rossumur/Zorkduino/zorkduino/zdFont.h

// 256 char inverted set
0x00,0x18,0x03,0x18,0x18,0x00,0x03,0xc0,
0x01,0x00,0x80,0x0f,0xf0,0xff,0x00,0x00,
0x24,0x28,0x08,0x10,0x10,0x10,0x08,0x08,
0x08,0x08,0x08,0x00,0x00,0x00,0x00,0x00,
0x00,0x00,0x00,0x00,0x18,0x00,0x1c,0x00,
0x00,0x00,0x00,0x00,0x00,0x00,0x00,0x00,
0x00,0x00,0x00,0x00,0x00,0x00,0x00,0x00,
0x00,0x00,0x00,0x00,0x06,0x00,0x60,0x00,
0x00,0x00,0x00,0x00,0x00,0x00,0x00,0x00,
0x00,0x00,0x00,0x00,0x00,0x00,0x00,0x00,
0x00,0x00,0x00,0x00,0x00,0x00,0x00,0x00,
0x00,0x00,0x00,0x00,0x00,0x00,0x00,0x00,
0x00,0x00,0x00,0x00,0x00,0x00,0x00,0x00,
0x00,0x00,0x00,0x00,0x00,0x00,0x00,0x00,
0x00,0x00,0x00,0x00,0x00,0x00,0x00,0x00,
0x00,0x00,0x00,0x00,0x18,0x00,0x08,0x10,
0xff,0xe7,0xfc,0xe7,0xe7,0xff,0xfc,0x3f,
0xfe,0xff,0x7f,0xf0,0x0f,0x00,0xff,0xff,
0xff,0xff,0xff,0xe7,0xff,0xff,0x3f,0xff,
0xe7,0x0f,0xe7,0x87,0xff,0xff,0xff,0xff,
0xff,0xff,0xff,0xff,0xe7,0xff,0xe3,0xff,
0xff,0xff,0xff,0xff,0xff,0xff,0xff,0xff,
0xff,0xff,0xff,0xff,0xff,0xff,0xff,0xff,
0xff,0xff,0xff,0xff,0xf9,0xff,0x9f,0xff,
0xff,0xff,0xff,0xff,0xff,0xff,0xff,0xff,
0xff,0xff,0xff,0xff,0xff,0xff,0xff,0xff,
0xff,0xff,0xff,0xff,0xff,0xff,0xff,0xff,
0xff,0xff,0xff,0xff,0xff,0xff,0xff,0xff,
0xff,0xff,0xff,0xff,0xff,0xff,0xff,0xff,
0xff,0xff,0xff,0xff,0xff,0xff,0xff,0xff,
0xff,0xff,0xff,0xff,0xff,0xff,0xff,0xff,
0xff,0xff,0xff,0xff,0xe7,0xff,0xf7,0xef,

0x00,0x18,0x03,0x18,0x18,0x00,0x07,0xe0,
0x03,0x00,0xc0,0x0f,0xf0,0xff,0x00,0x00,
0x00,0x00,0x10,0x08,0x08,0x08,0x14,0x14,
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
0xff,0xff,0xff,0xff,0xff,0xff,0xff,0xff,
0xff,0xff,0xff,0xff,0xff,0xff,0xff,0xff,
0xff,0xff,0xff,0xff,0xff,0xff,0xff,0xff,
0xff,0xff,0xff,0xff,0xff,0xff,0xff,0x83,
0xff,0xff,0xc3,0xff,0xff,0xff,0xff,0xff,
0x9f,0xf9,0xff,0xff,0xff,0xff,0xff,0xff,
0xff,0x87,0xff,0xff,0xe7,0xff,0xff,0xff,
