rossumur/Zorkduino/zorkduino/zdLogofont.h

// 200x72 256 chars
0x00,0x00,0x00,0x00,0x00,0x00,0x00,0x00,
0x00,0x00,0x00,0x00,0x00,0x00,0x00,0x00,
0x00,0x00,0x00,0x00,0x02,0xf8,0xc4,0x00,
0x00,0x00,0x00,0x00,0x00,0x00,0x00,0x00,
0x00,0x00,0x00,0x7c,0x80,0x00,0x00,0x00,
0x00,0x00,0x00,0x00,0x00,0x04,0x4f,0xf0,
0x00,0x00,0x00,0x00,0x08,0xef,0xff,0x7e,
0x5b,0xd6,0x00,0x04,0x04,0x17,0xc1,0xff,
0x81,0x64,0x4b,0xfb,0x39,0xfa,0x06,0xf7,
0xf8,0x00,0x10,0xe2,0x00,0x0b,0xed,0x8f,
0x57,0xc0,0xf4,0x52,0xf0,0xef,0xb8,0x01,
0xfd,0xe0,0x00,0xe7,0xf8,0xf5,0x7d,0x89,
0xff,0xe6,0x03,0x2a,0x00,0x00,0x00,0x00,
0x00,0x7f,0x9f,0xe0,0x00,0x00,0x21,0x41,
0xe1,0xff,0xf8,0x18,0x68,0x00,0x7f,0xfe,
0x02,0xf7,0x0c,0x7b,0xd2,0x00,0x00,0x00,
0x00,0x19,0x99,0x80,0x00,0x00,0x44,0x40,
0xc0,0x48,0xfc,0xe0,0x34,0xc1,0x09,0xfe,
0x60,0x01,0x48,0xa0,0x05,0xde,0xc0,0x00,
0x03,0xef,0x66,0x60,0x00,0x00,0x00,0x00,
0x00,0xf4,0x01,0xd2,0x90,0x3e,0x08,0x00,
0x57,0xfe,0x82,0x13,0xf8,0x3a,0x5c,0x00,
0x00,0x13,0xd9,0xff,0xbf,0xfb,0x86,0x25,
0x7e,0xf9,0xcf,0x21,0x3c,0xc0,0x67,0xfd,
0x80,0x93,0x7f,0xc1,0xfa,0x80,0x03,0x16,
0xbe,0x00,0x00,0xdf,0xc2,0x7e,0x02,0x32,
0xe0,0xad,0x81,0x40,0x01,0x00,0x00,0x28,
0x02,0x00,0x21,0xff,0x40,0xce,0xbc,0x00,
0xd0,0x1f,0x80,0x00,0x00,0x00,0x00,0x00,
0x00,0x00,0x00,0x00,0x00,0x00,0x00,0x00,
0x00,0x00,0x00,0x00,0x00,0x00,0x00,0x00,
0x00,0x00,0x00,0x00,0x00,0x00,0x00,0x00,

0x00,0x00,0x00,0x00,0x00,0x00,0x00,0x00,
0x00,0x00,0x00,0x00,0x00,0x00,0x00,0x00,
0x00,0x00,0x00,0x00,0x0c,0x2e,0xc4,0x00,
0x00,0x00,0x00,0x00,0x00,0x00,0x00,0x00,
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
0x07,0xe0,0x00,0x00,0x00,0x00,0x00,0x00,
0x00,0x00,0x00,0x02,0x30,0x00,0x00,0x00,
0x00,0x00,0x00,0x00,0x00,0x00,0x00,0x00,
0x00,0x00,0x00,0x00,0x00,0x00,0x00,0x00,
0x00,0x00,0x00,0x00,0x00,0x00,0x00,0x00,
0x00,0x00,0x00,0x00,0x00,0x00,0x00,0x00,
0x00,0x00,0x00,0x00,0x00,0x00,0x00,0x00,
